kamratia1/FYP_2015/Microcontroller Files/STM32/Target_options.pdf

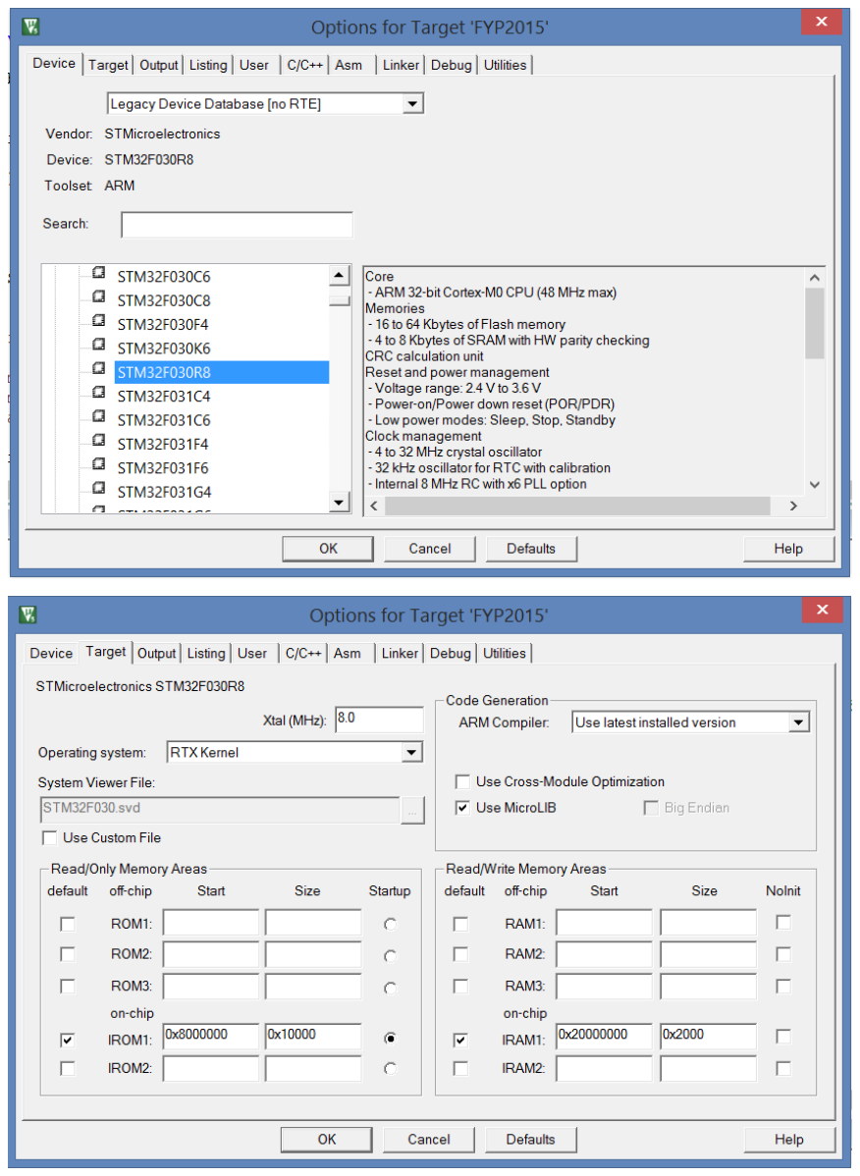
[picture p2: page 1]
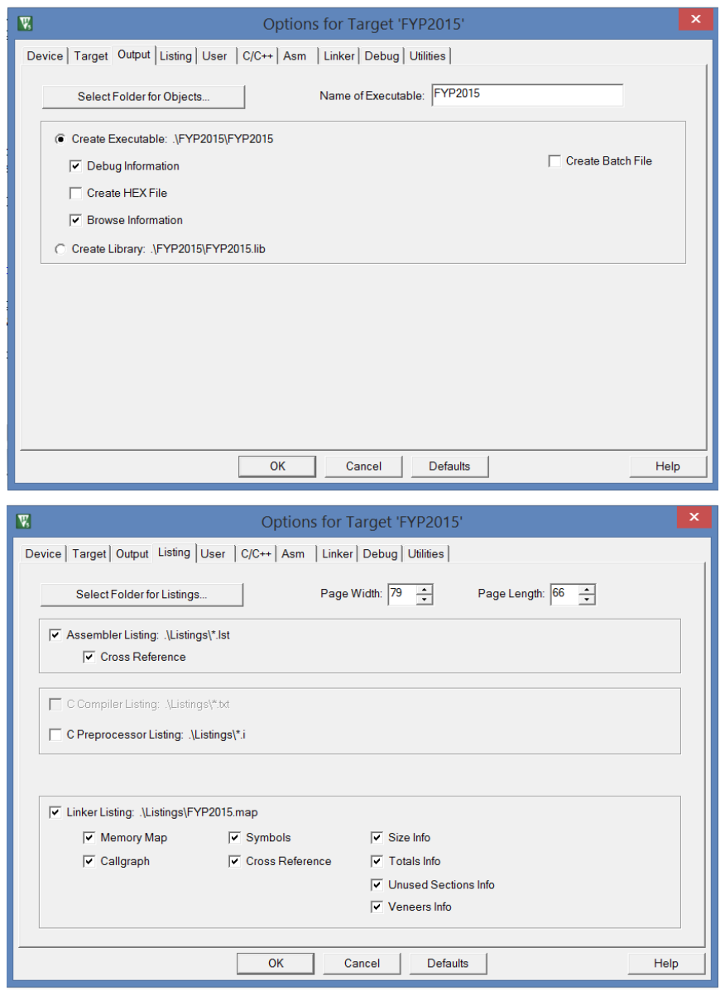
[picture p3: page 2]
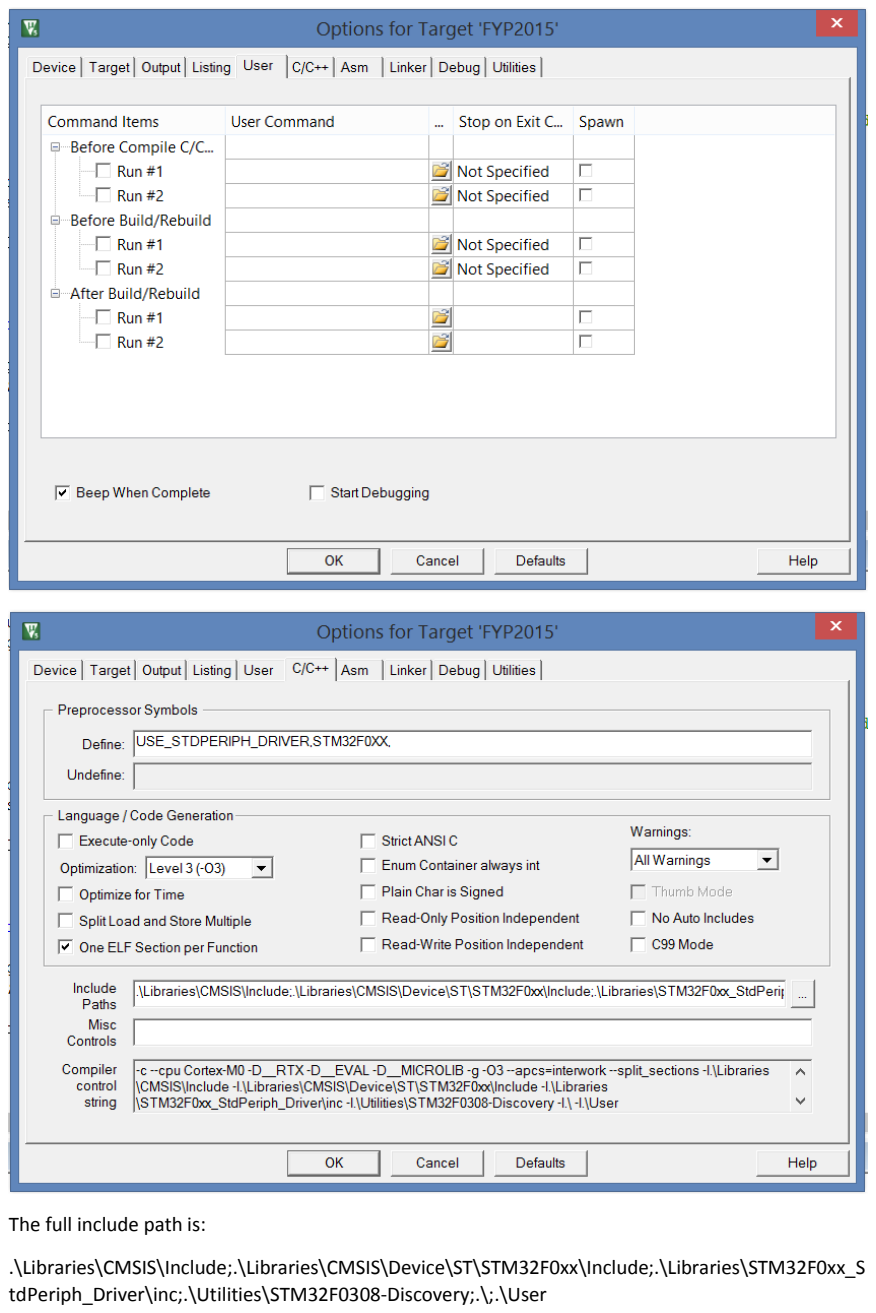
[picture p4: page 3]

The full include path is:

.\Libraries\CMSIS\Include;.\Libraries\CMSIS\Device\ST\STM32F0xx\Include;.\Libraries\STM32F0xx_S tdPeriph_Driver\inc;.\Utilities\STM32F0308-Discovery;.\;.\User

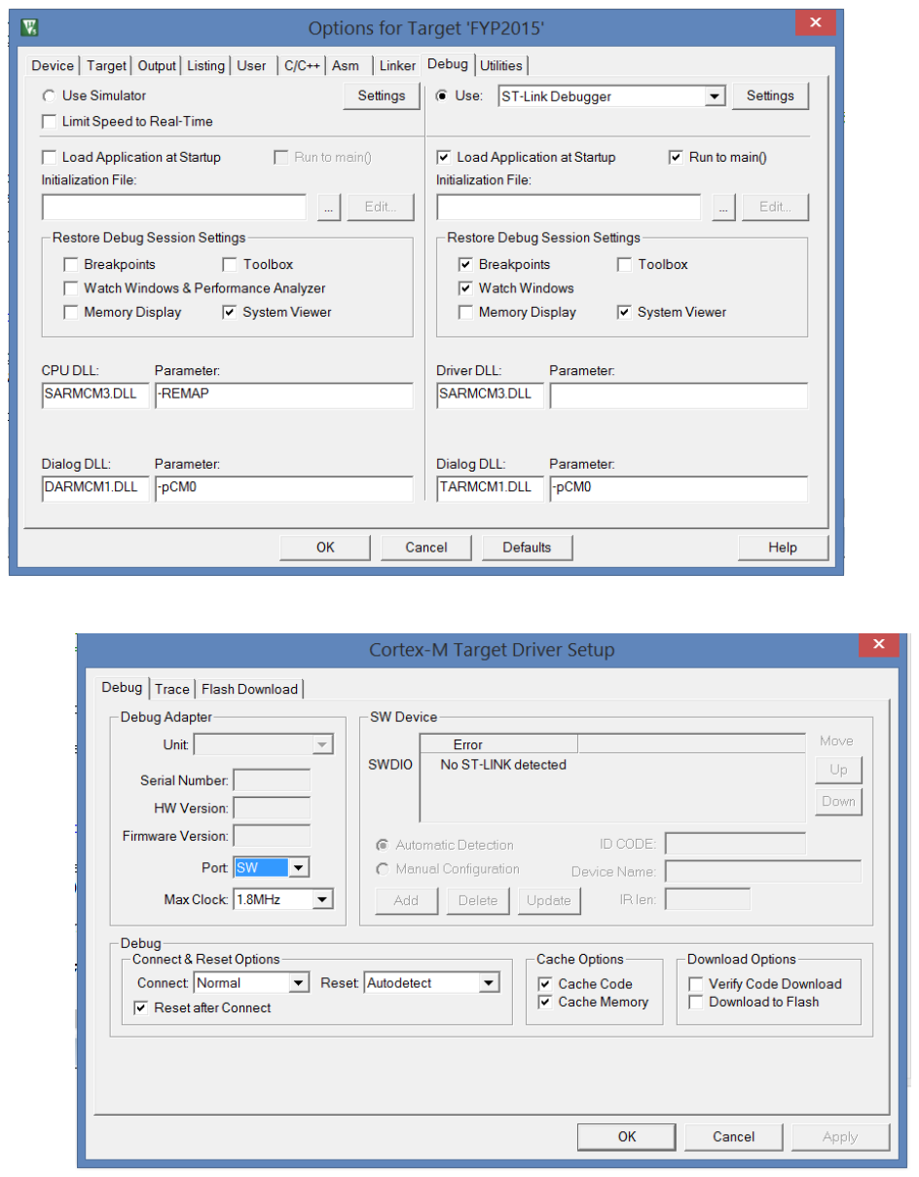
[picture p5: page 4]

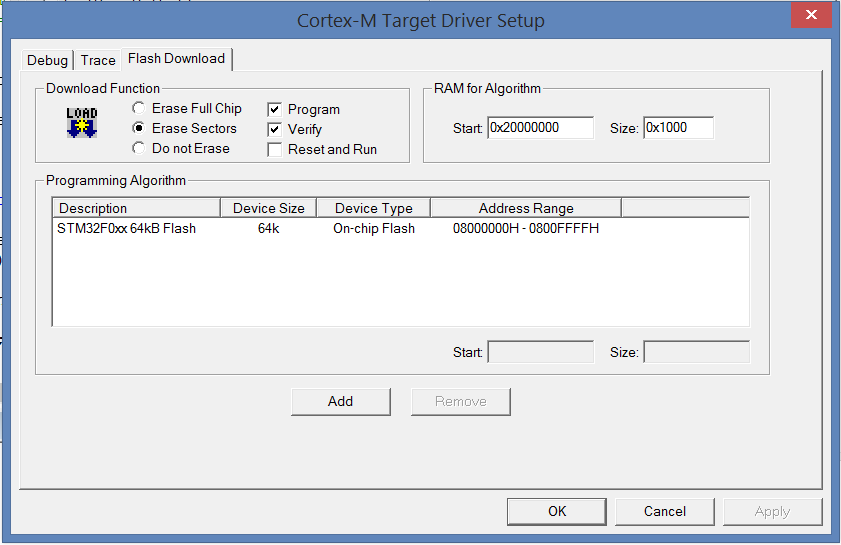
[picture p6: figure]
