kamratia1/FYP_2015/PCB Design Files/Simulation/FYP_HVConv.asc

C1: cap; 4.7µF
C2: cap; 4.7µ; V=250 Rser=0.001
C3: cap; 33p
C4: cap; 100p
C5: cap; 50n
D1: diode; GSD2004W-V
D2: schottky; B540C
D3: schottky; MBRS360
L1: ind2; 15µ; Ipk=10 Rser=0
L2: ind2; 3375µ; Rser=0
M1: nmos; AP9465GEM
R1: res; 10Meg
R2: res; 100k
R3: res; 10k
R4: res; 10k
R5: res; 100k
R6: res; 20k
R7: res; 1
R8: res; 25
R9: res; 40k; pwr=0.1
U1: LT3468
U3: UniversalOpamp2; Avol=1Meg GBW=2.8Meg Slew=1Meg
V1: voltage; 3V
V3: voltage; PULSE(0 5 0 1n 1n 0.00125 0.0025)
V4: voltage; {X}
Named nets: 0, DONE, VIN, CHARGE, V_ADJUST, FB, SW, VOUT
K L1 L2 0.9899.
.tran 0.1 startup
.step param X list 0.3 0.5 0.7 0.9
