kamratia1/FYP_2015/Microcontroller Files/STM32/User/timer.c

#include "timer.h"

__IO uint16_t CCR3_Val = 1600;
uint16_t PrescalerValue = 0;
uint16_t PrescalerValue2 = 0;

void TIM3_Config(uint16_t freq)
{
  TIM_TimeBaseInitTypeDef  TIM_TimeBaseStructure;
  TIM_OCInitTypeDef  TIM_OCInitStructure;
  NVIC_InitTypeDef NVIC_InitStructure;
	
  /* TIM3 clock enable */
  RCC_APB1PeriphClockCmd(RCC_APB1Periph_TIM3, ENABLE);

  /* Enable the TIM3 gloabal Interrupt */
  NVIC_InitStructure.NVIC_IRQChannel = TIM3_IRQn;
  NVIC_InitStructure.NVIC_IRQChannelPriority = 0;
  NVIC_InitStructure.NVIC_IRQChannelCmd = ENABLE;
  NVIC_Init(&NVIC_InitStructure);
  
  /* -----------------------------------------------------------------------
    TIM3 Configuration: Output Compare Timing Mode:
    
    In this example TIM3 input clock (TIM3CLK) is set to APB1 clock (PCLK1),  
      => TIM3CLK = PCLK1 = SystemCoreClock = 48 MHz
          
    To get TIM3 counter clock at 6 MHz, the prescaler is computed as follows:
       Prescaler = (TIM3CLK / TIM3 counter clock) - 1
       Prescaler = (PCLK1 /6 MHz) - 1
                                                  
    CC3 update rate = TIM3 counter clock / CCR3_Val = 439.4 Hz

    Note: 
     SystemCoreClock variable holds HCLK frequency and is defined in system_stm32f2xx.c file.
     Each time the core clock (HCLK) changes, user had to call SystemCoreClockUpdate()
     function to update SystemCoreClock variable value. Otherwise, any configuration
     based on this variable will be incorrect.    
  ----------------------------------------------------------------------- */   

  /* Compute the prescaler value */
  PrescalerValue = (uint16_t) (SystemCoreClock  / 6000000) - 1;

  /* Time base configuration */
  TIM_TimeBaseStructure.TIM_Period = 65535;
  TIM_TimeBaseStructure.TIM_Prescaler = 0;
  TIM_TimeBaseStructure.TIM_ClockDivision = 0;
  TIM_TimeBaseStructure.TIM_CounterMode = TIM_CounterMode_Up;

  TIM_TimeBaseInit(TIM3, &TIM_TimeBaseStructure);

  /* Prescaler configuration */
  TIM_PrescalerConfig(TIM3, PrescalerValue, TIM_PSCReloadMode_Immediate);

  /* Output Compare Timing Mode configuration: Channel1 */
  TIM_OCInitStructure.TIM_OCMode = TIM_OCMode_Timing;
  TIM_OCInitStructure.TIM_OCPolarity = TIM_OCPolarity_High;
	
	CCR3_Val = 6000000/freq;
  /* Output Compare Timing Mode configuration: Channel3 */
  TIM_OCInitStructure.TIM_OutputState = TIM_OutputState_Enable;
  TIM_OCInitStructure.TIM_Pulse = CCR3_Val;
	
  TIM_OC3Init(TIM3, &TIM_OCInitStructure);

  TIM_OC3PreloadConfig(TIM3, TIM_OCPreload_Disable);

  /* TIM Interrupts enable */
  TIM_ITConfig(TIM3, TIM_IT_CC3, ENABLE);

  /* TIM3 enable counter */
  TIM_Cmd(TIM3, ENABLE);
}

void TIM2_Config(void)
{
	// Setup a Counter for time measurement
	TIM_TimeBaseInitTypeDef  TIM_TimeBaseStructure;
	
	RCC_APB1PeriphClockCmd(RCC_APB1Periph_TIM2, ENABLE);
	
	PrescalerValue2 = (uint16_t) (SystemCoreClock  / 6000000) - 1;
	
	 /* Time base configuration */
  TIM_TimeBaseStructure.TIM_Period = 0xFFFFFFFF;
  TIM_TimeBaseStructure.TIM_Prescaler = 0;
  TIM_TimeBaseStructure.TIM_ClockDivision = 0;
  TIM_TimeBaseStructure.TIM_CounterMode = TIM_CounterMode_Up;
		
		
	TIM_TimeBaseInit(TIM2, &TIM_TimeBaseStructure);
	
	/* Prescaler configuration */
  TIM_PrescalerConfig(TIM2, PrescalerValue2, TIM_PSCReloadMode_Immediate);

	TIM_Cmd(TIM2, ENABLE);
	
}
