kamratia1/FYP_2015/Microcontroller Files/STM32/User/timer.h

#ifndef __timer_h_
#define __timer_h_

#include "config.h"

/* Private function prototypes -----------------------------------------------*/
void TIM3_Config(uint16_t);
void TIM2_Config(void);

#endif
